mirage335/PWMController/productionStatic/hacdcCNC/PWMController/outp1_original_front.png

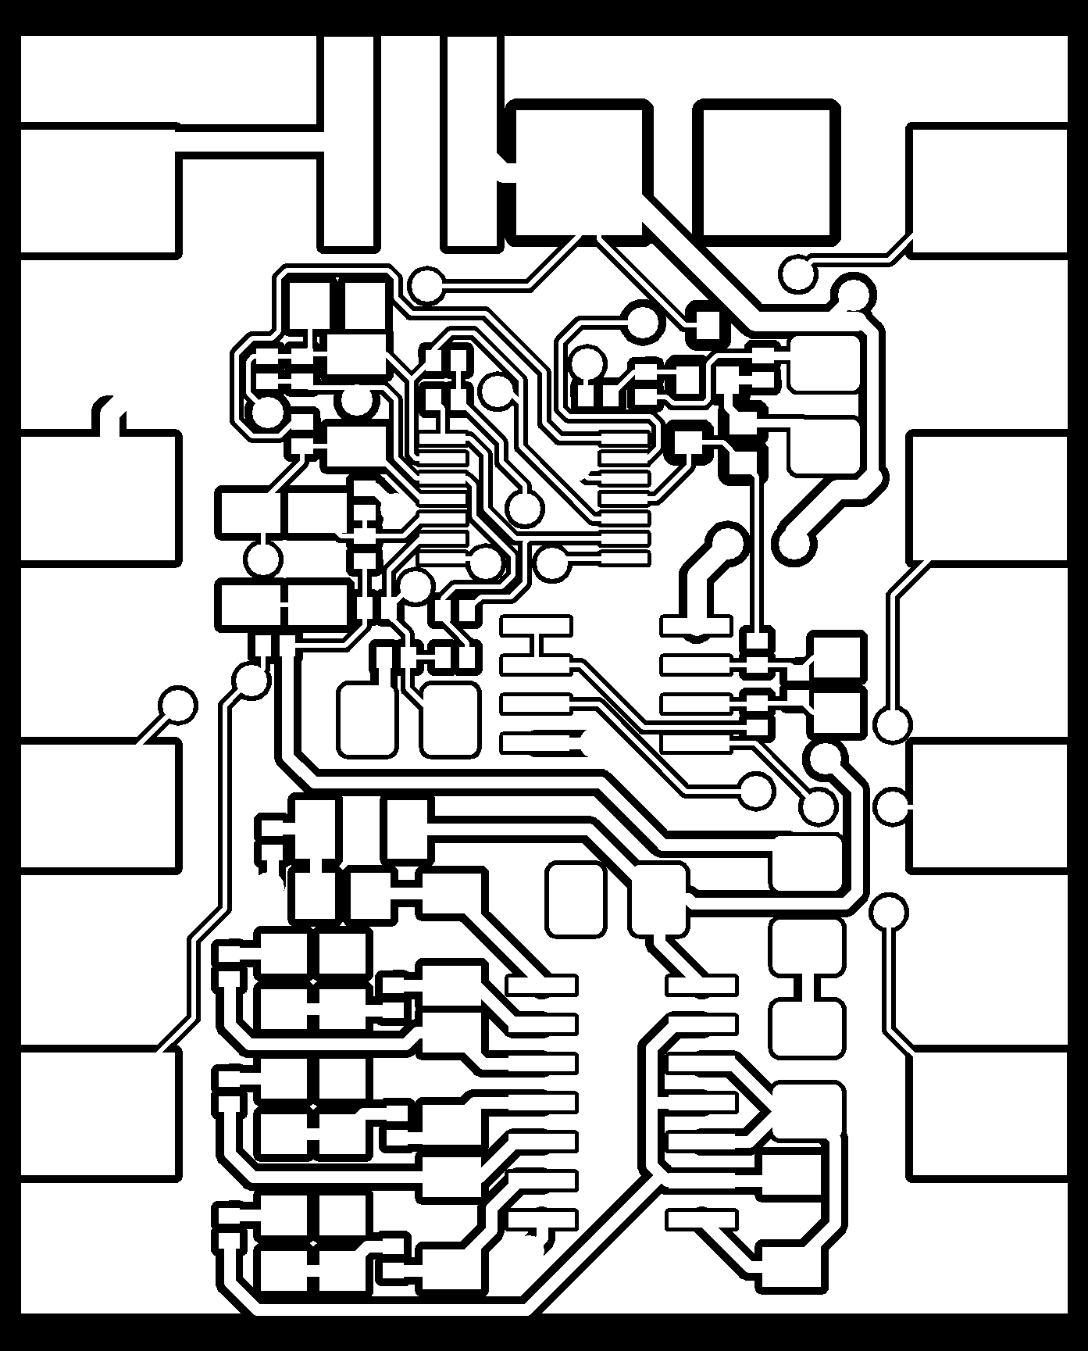
productionStatic/hacdcCNC/PWMController/outp1_original_front.png
