mirage335/PWMController/productionStatic/hacdcCNC/PWMController/outp2_original_outline.png

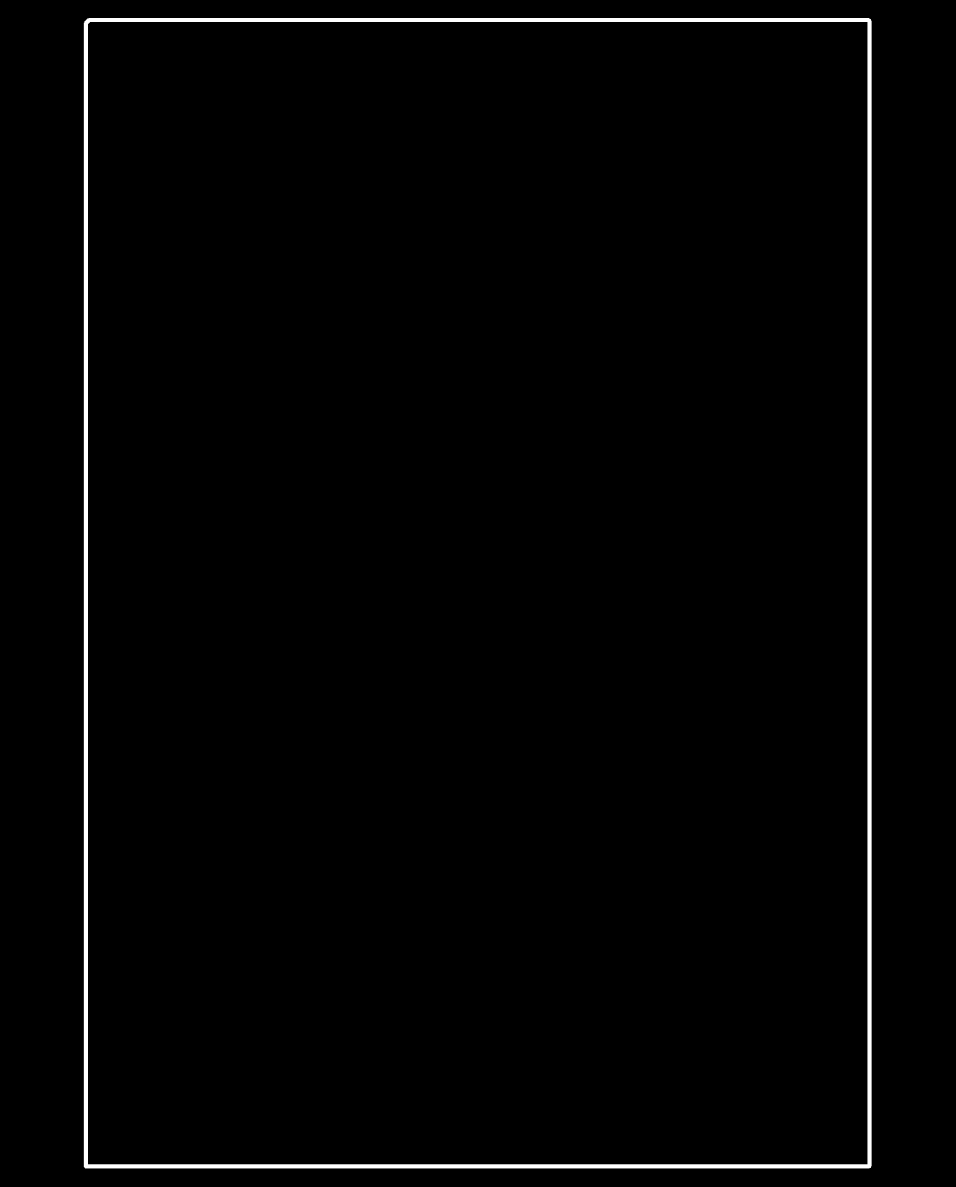
productionStatic/hacdcCNC/PWMController/outp2_original_outline.png
