mirage335/PWMController/productionStatic/hacdcCNC/PWMController/outp3_outline_filled.png

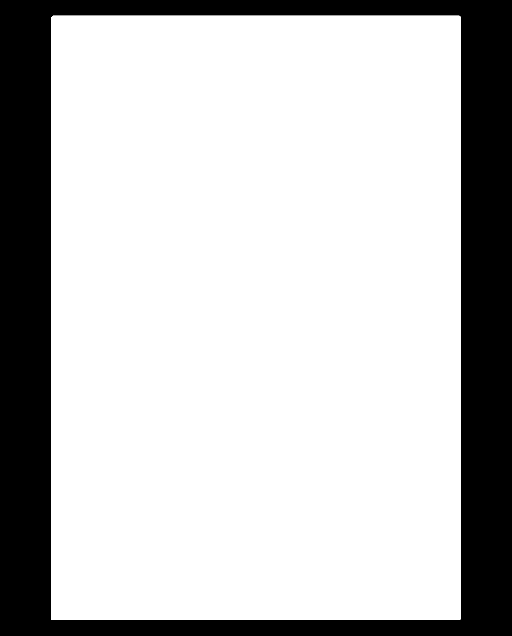
productionStatic/hacdcCNC/PWMController/outp3_outline_filled.png
